jingyi679/Strawberry_FE/models/OpenMV H7 Camera mount technical drawing.png

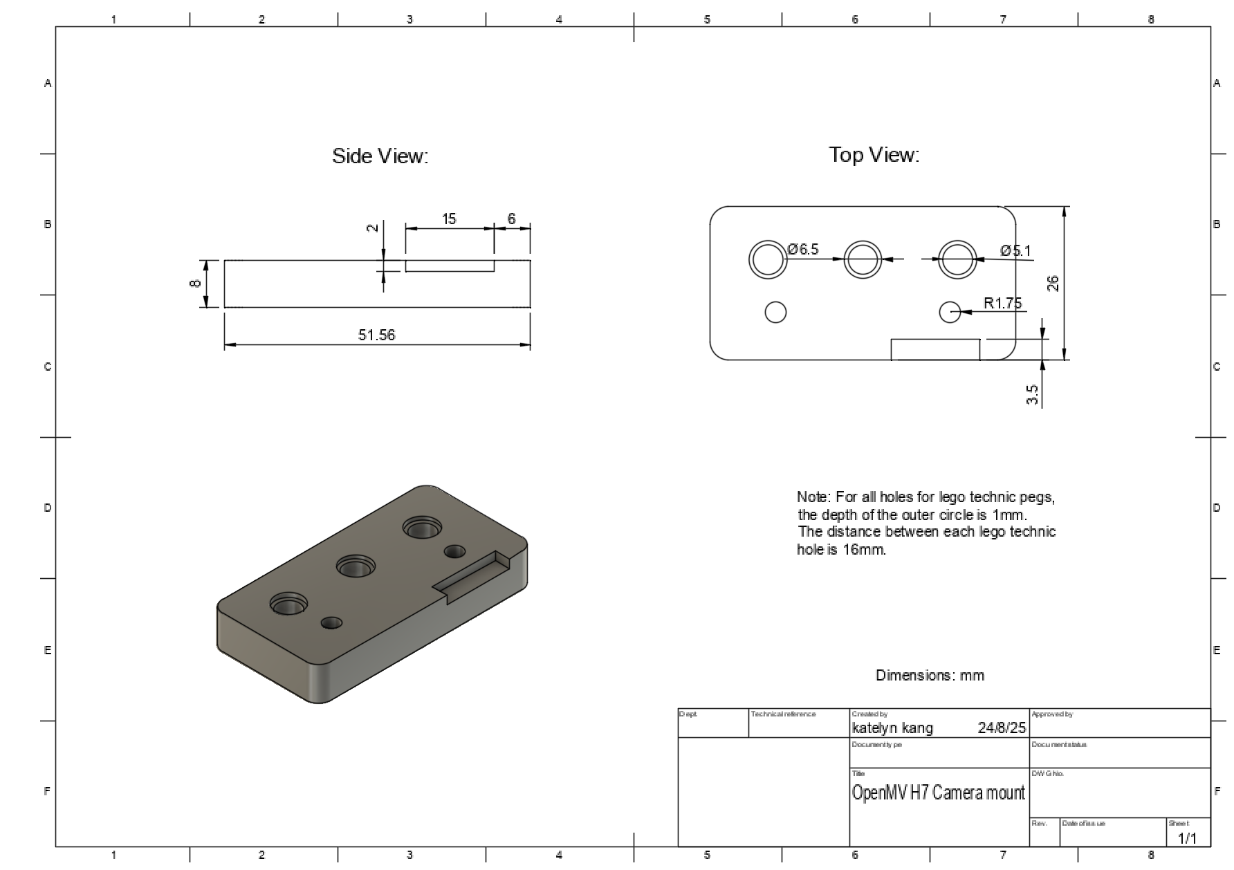
models/OpenMV H7 Camera mount technical drawing.png
