jingyi679/Strawberry_FE/v-photos/back.jpg

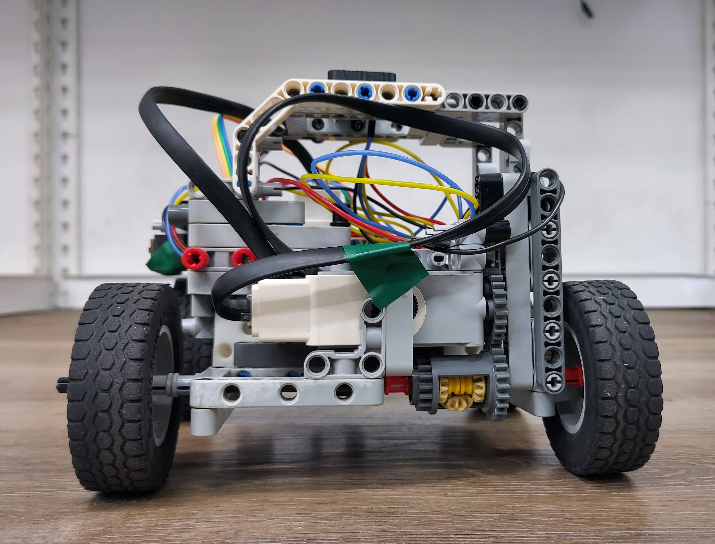
v-photos/back.jpg
