jingyi679/Strawberry_FE/v-photos/front.jpg

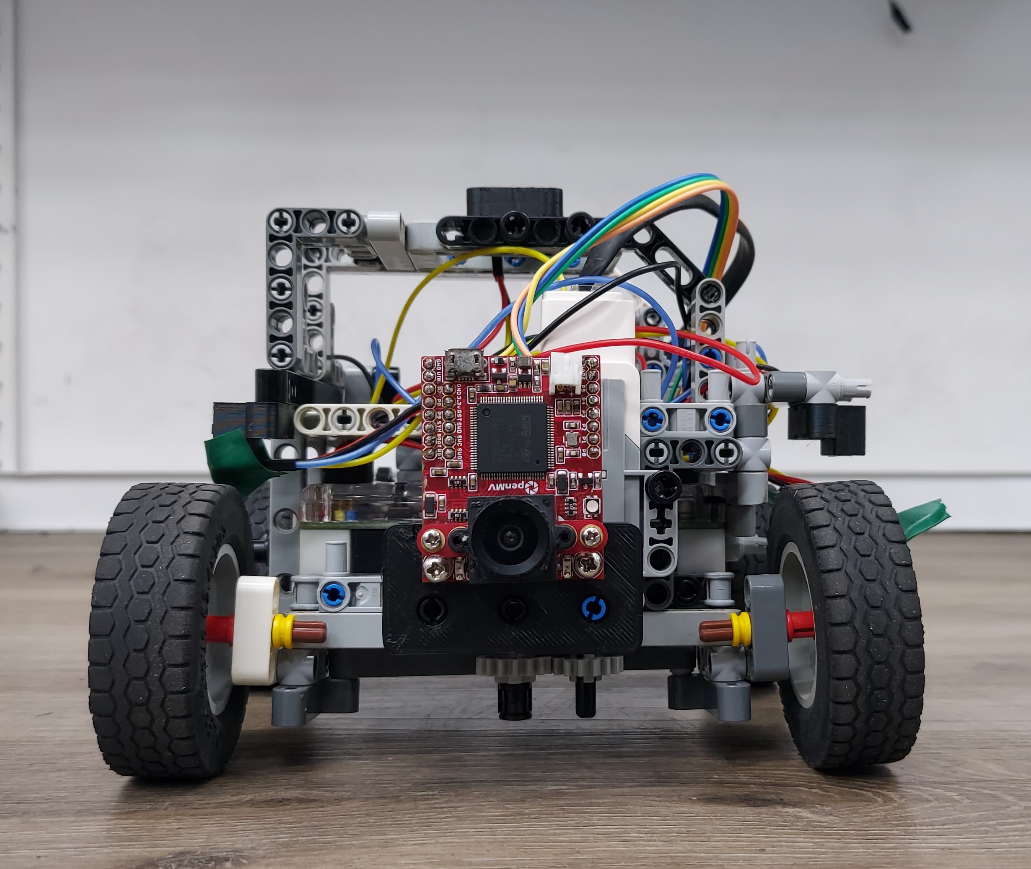
v-photos/front.jpg
