jingyi679/Strawberry_FE/v-photos/right.jpg

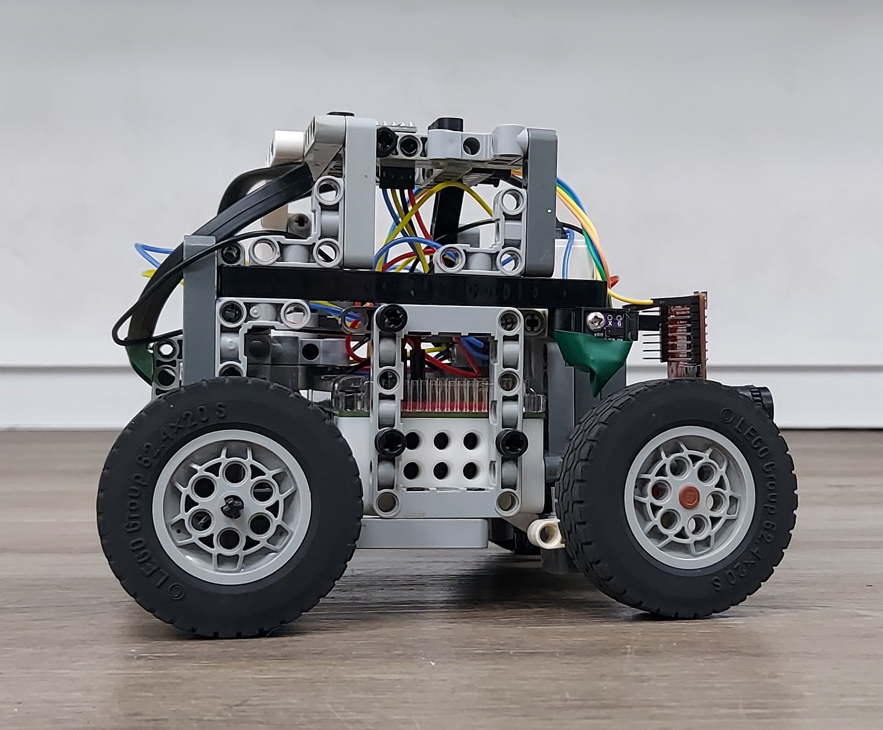
v-photos/right.jpg
