jingyi679/Strawberry_FE/v-photos/top.jpg

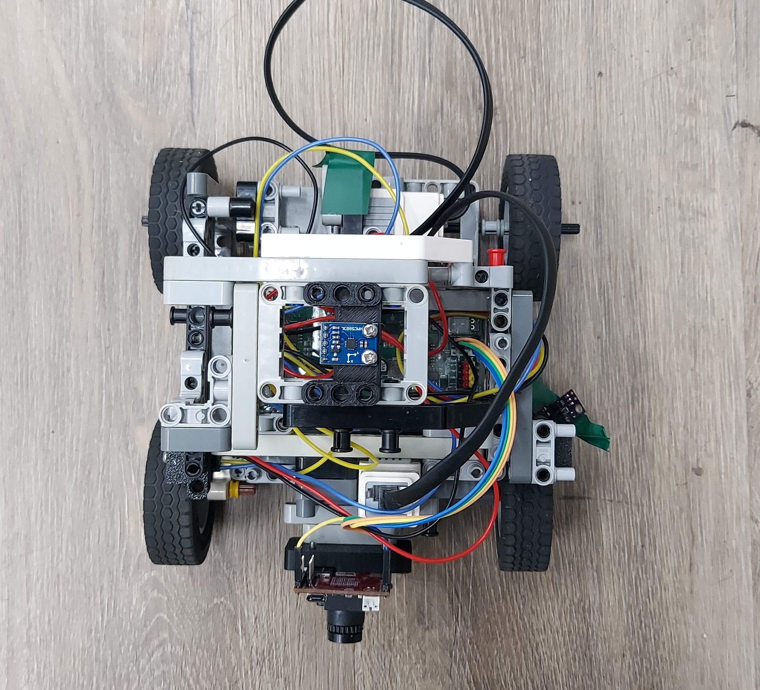
v-photos/top.jpg
