jingyi679/Strawberry_FE/schemes/Block diagram for wiring.png

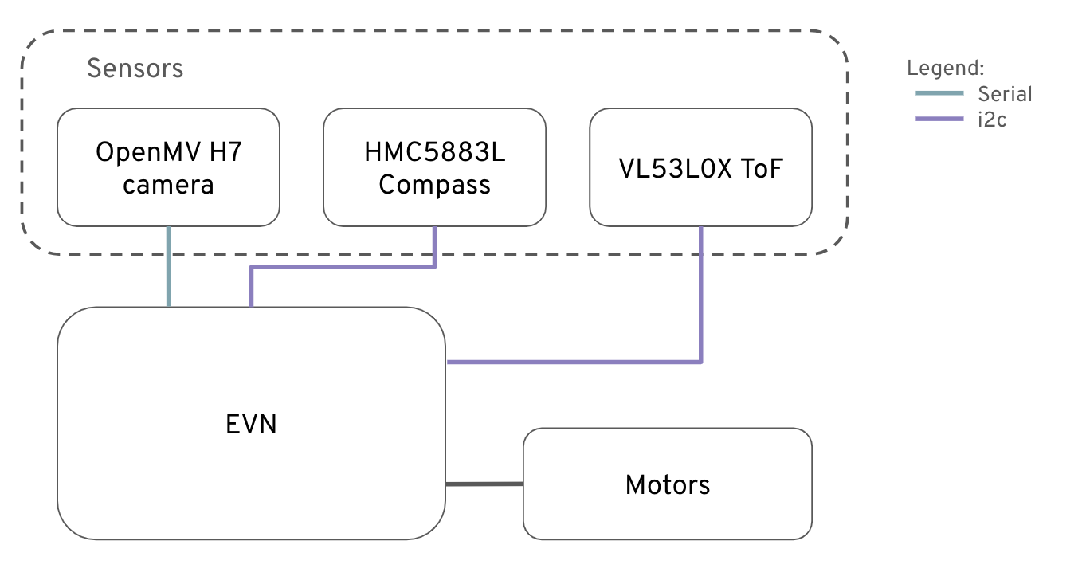
schemes/Block diagram for wiring.png
